dilshan/6ch-af-preamplifier/resources/6ch-wire-diagram/6ch-wire-diagram.sch

## KiCad design resources/6ch-wire-diagram/6ch-wire-diagram.sch (2021-11-01)

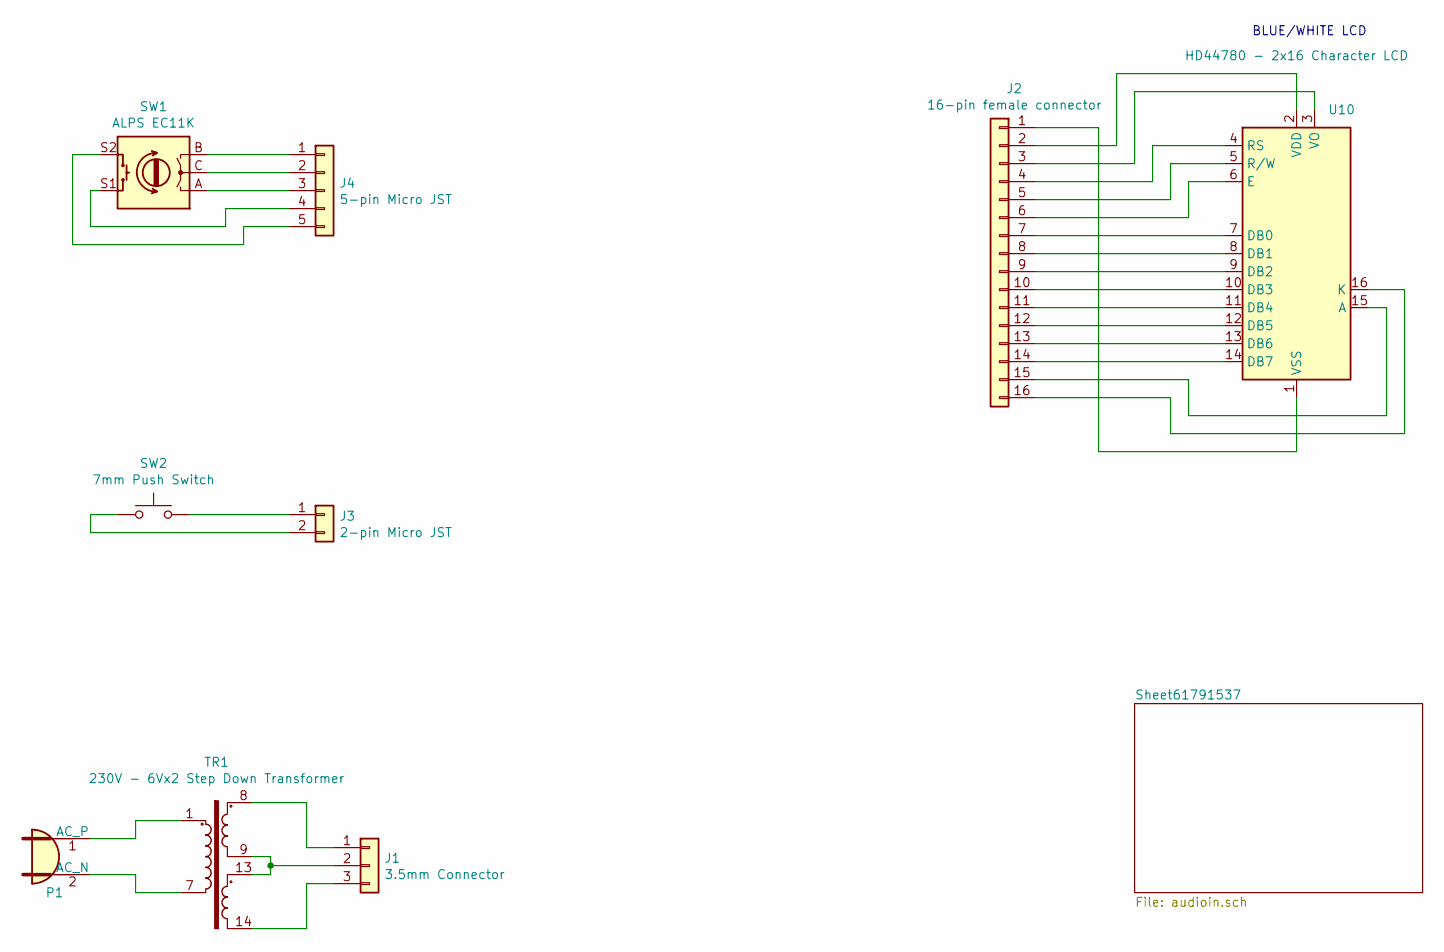
[picture p20: schematic 6ch-wire-diagram.sch]

Parts:
J1: 3.5mm Connector
J2: 16-pin female connector
J3: 2-pin Micro JST
J4: 5-pin Micro JST
P1: (no value)
SW1: ALPS EC11K
SW2: 7mm Push Switch
TR1: 230V - 6Vx2 Step Down Transformer; Transformer_Breve_TEZ-47x57
U10: HD44780 - 2x16 Character LCD; NHD-0420H1Z

Connections:
unnamed: J1.1, TR1.8
unnamed: J1.2, TR1.9, TR1.13
unnamed: J1.3, TR1.14
unnamed: J2.1, U10.1 (VSS)
unnamed: J2.2, U10.2 (VDD)
unnamed: J2.3, U10.3 (VO)
unnamed: J2.4, U10.4 (RS)
unnamed: J2.5, U10.5 (R/W)
unnamed: J2.6, U10.6 (E)
unnamed: J2.7, U10.7 (DB0)
unnamed: J2.8, U10.8 (DB1)
unnamed: J2.9, U10.9 (DB2)
unnamed: J2.10, U10.10 (DB3)
unnamed: J2.11, U10.11 (DB4)
unnamed: J2.12, U10.12 (DB5)
unnamed: J2.13, U10.13 (DB6)
unnamed: J2.14, U10.14 (DB7)
unnamed: J2.15, U10.15 (A)
unnamed: J2.16, U10.16 (K)
unnamed: J3.1, SW2.2
unnamed: J3.2, SW2.1
unnamed: J4.1, SW1.B
unnamed: J4.2, SW1.C
unnamed: J4.3, SW1.A
unnamed: J4.4, SW1.S1
unnamed: J4.5, SW1.S2
unnamed: P1.1 (AC_P), TR1.1
unnamed: P1.2 (AC_N), TR1.7

Notes on the sheet:
BLUE/WHITE LCD
