dilshan/6ch-af-preamplifier/resources/6ch-wire-diagram/audioin.sch

## KiCad design resources/6ch-wire-diagram/audioin.sch (2021-11-01)

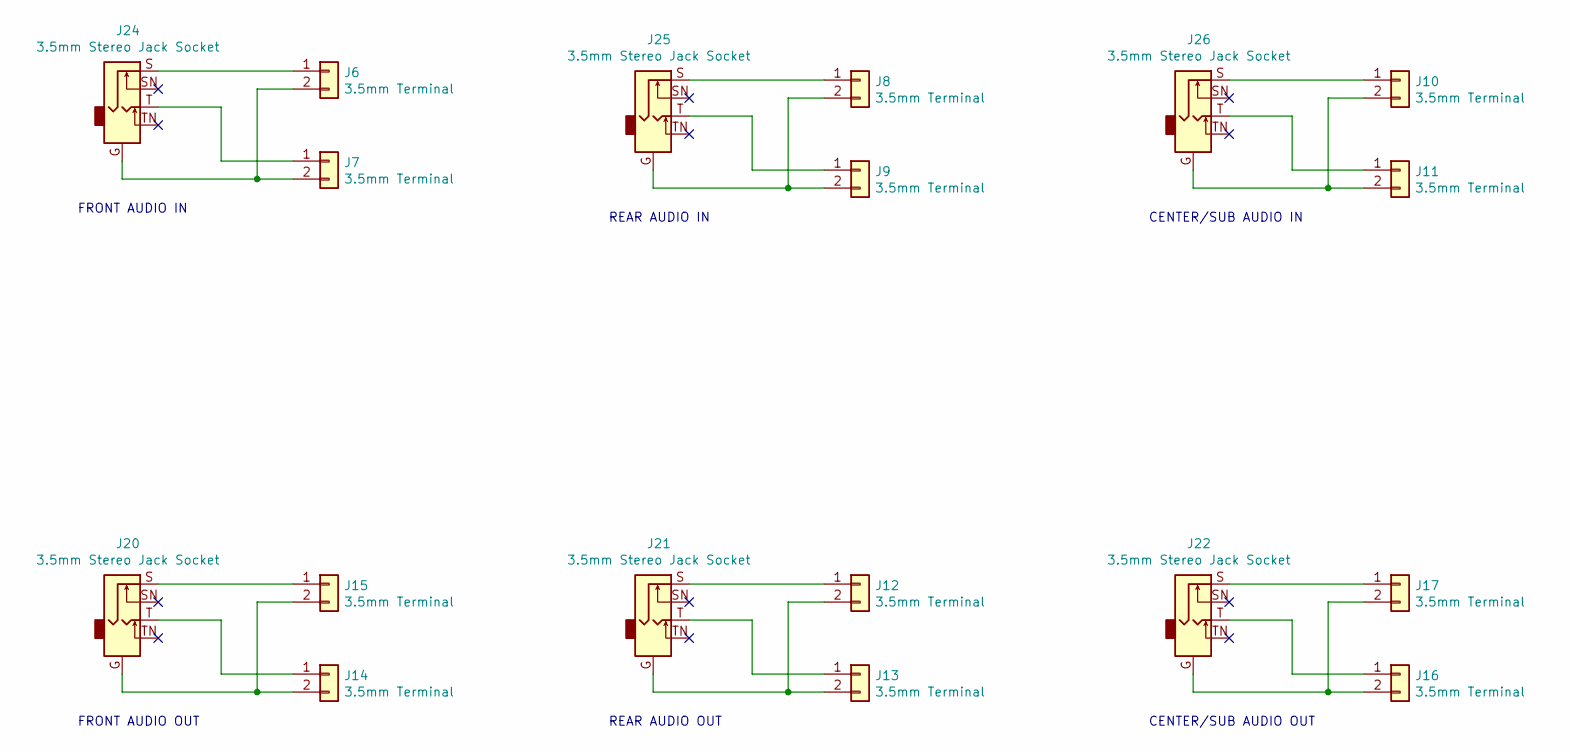
[picture p21: schematic audioin.sch]

Parts:
J6, J7, J8, J9, J10, J11, J12, J13, J14, J15, J16, J17: 3.5mm Terminal
J20, J21, J22, J24, J25, J26: 3.5mm Stereo Jack Socket

Connections:
unnamed: J10.1, J26.S
unnamed: J10.2, J11.2, J26.G
unnamed: J11.1, J26.T
unnamed: J12.1, J21.S
unnamed: J12.2, J13.2, J21.G
unnamed: J13.1, J21.T
unnamed: J14.1, J20.T
unnamed: J14.2, J15.2, J20.G
unnamed: J15.1, J20.S
unnamed: J16.1, J22.T
unnamed: J16.2, J17.2, J22.G
unnamed: J17.1, J22.S
unnamed: J6.2, J7.2, J24.G
unnamed: J6.1, J24.S
unnamed: J7.1, J24.T
unnamed: J8.2, J9.2, J25.G
unnamed: J8.1, J25.S
unnamed: J9.1, J25.T

Notes on the sheet:
FRONT AUDIO IN
REAR AUDIO IN
CENTER/SUB AUDIO IN
FRONT AUDIO OUT
REAR AUDIO OUT
CENTER/SUB AUDIO OUT
